logordon/SENSE/Project Images/rpi_view_top.JPG

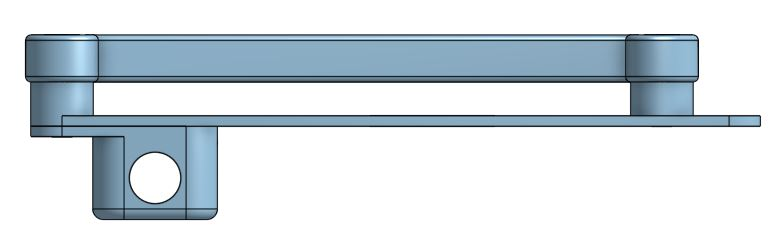
Project Images/rpi_view_top.JPG
