logordon/SENSE/Project Images/sensor_view_top.JPG

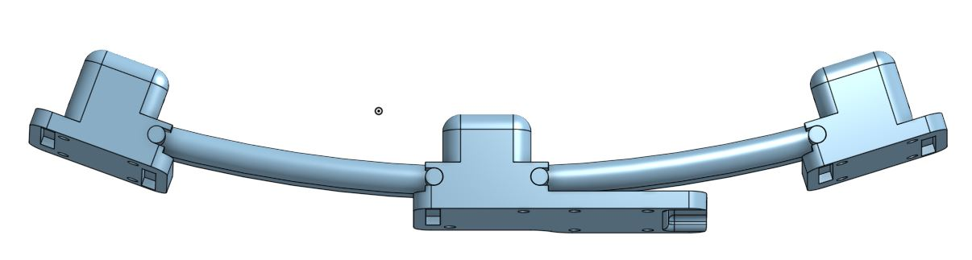
Project Images/sensor_view_top.JPG
