logordon/SENSE/Project Images/Wiring Schematic.JPG

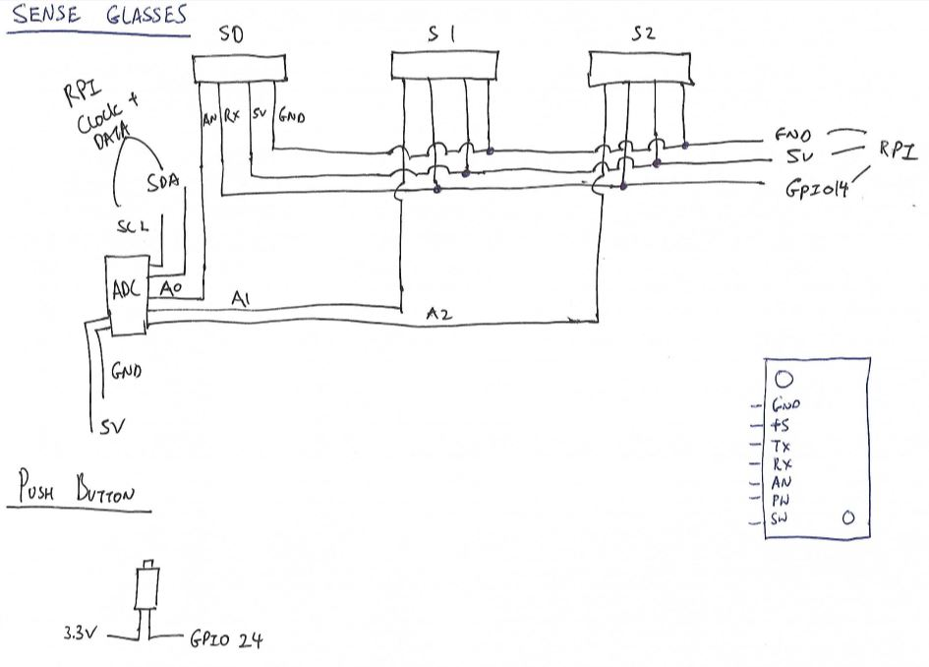
Project Images/Wiring Schematic.JPG
